NotGormi/Taller_Diseno_Grupo11/iteraciones/iteracion_1/README.md

# Iteración 1 - Concepto Inicial

## Información General

**Fecha:** [23/04/2025]  
**Versión:** v1.0  
**Estado:** Prototipo alpha - Prueba de concepto  
**Avance asociado:** Planificación inicial / Avance #1

---

## Descripción

Primera versión del prototipo, enfocada en validar la factibilidad técnica del concepto.

**Objetivo de esta iteración:**
- Probar conexión de sensores básicos
- Validar comunicación con microcontrolador
- Demostrar concepto de actuación
- Circuito básico en protoboard

---

## Componentes Utilizados

### Hardware
- Microcontrolador: [Modelo]
- Sensores:
  - [Sensor 1]
  - [Sensor 2]
- Actuadores:
  - [Actuador 1]
- Otros: [Lista]

### Software
- IDE: Arduino IDE
- Librerías: [Lista]
- Versión código: v1.0

---

## Fotos del Prototipo

Incluir en esta carpeta:
- `v1_circuito_protoboard.jpg`
- `v1_vista_general.jpg`
- `v1_detalle_conexiones.jpg`

---

## Resultados de Testing Inicial

### Funcionalidad Lograda
✅ [Función 1]  
✅ [Función 2]  
❌ [Función 3 - no funcionó]

### Problemas Identificados

1. **Problema 1:**
   - Descripción: [Detalles]
   - Causa probable: [Análisis]
   - Solución propuesta: [Plan]

2. **Problema 2:**
   - Descripción: [Detalles]
   - Causa probable: [Análisis]
   - Solución propuesta: [Plan]

---

## Aprendizajes

### Técnicos
- [Aprendizaje 1]
- [Aprendizaje 2]

### De Diseño
- [Aprendizaje 1]
- [Aprendizaje 2]

---

## Plan para Iteración 2

### Mejoras Planificadas

**Hardware:**
- [ ] [Mejora 1]
- [ ] [Mejora 2]

**Software:**
- [ ] [Mejora 1]
- [ ] [Mejora 2]

**Diseño:**
- [ ] Iniciar diseño de encapsulado
- [ ] Mejorar ruteo de cables

---

## Archivos en esta Carpeta

- `v1_codigo.ino` - Código de esta versión
- `v1_esquema.png` - Esquema del circuito
- `v1_fotos/` - Fotografías del prototipo
- `v1_notas.txt` - Notas adicionales del equipo
