NotGormi/Taller_Diseno_Grupo11/iteraciones/iteracion_2/README.md

# Iteración 2 - Primera Mejora Significativa

## Información General

**Fecha:** [21/05/2026]  
**Versión:** v2.0  
**Estado:** Prototipo funcional mejorado  
**Avance asociado:** Avance #2

---

## Descripción

Segunda versión del prototipo, incorporando feedback de la iteración 1 y del Avance #1. Incluye mejoras significativas en funcionalidad y primeros pasos en diseño de encapsulado.

**Objetivos de esta iteración:**
- Corregir problemas identificados en v1
- Agregar funcionalidades adicionales
- Iniciar diseño 3D del encapsulado
- Realizar primeras pruebas con usuarios

---

## Cambios Respecto a v1

### Hardware
**Agregado:**
- [Componente nuevo 1]
- [Componente nuevo 2]

**Modificado:**
- [Cambio 1] - Razón: [Justificación]
- [Cambio 2] - Razón: [Justificación]

**Removido:**
- [Componente removido] - Razón: [Justificación]

### Software
**Nuevas funcionalidades:**
- [Feature 1]
- [Feature 2]

**Optimizaciones:**
- [Optimización 1]
- [Optimización 2]

**Bugs corregidos:**
- [Bug 1 de v1]
- [Bug 2 de v1]

### Diseño Mecánico
- Primer diseño de encapsulado en Fusion 360
- Prototipo impreso en 3D
- Integración de componentes en carcasa

---

## Fotos del Prototipo v2

Incluir en esta carpeta:
- `v2_prototipo_completo.jpg`
- `v2_circuito_integrado.jpg`
- `v2_encapsulado_inicial.jpg`
- `v2_testing_usuario.jpg`

---

## Resultados de Testing

### Funcionalidad Lograda
✅ [Función 1]  
✅ [Función 2]  
✅ [Función 3]  
⚠️ [Función 4 - parcial]

### Feedback del Avance #2

**Comentarios del profesor/ayudante:**
1. [Comentario 1]
   - Acción: [Plan de mejora para v3]

2. [Comentario 2]
   - Acción: [Plan de mejora para v3]

### Testing con Usuarios (2-3 personas)

**Resultados cuantitativos:**
- Facilidad de uso promedio: [X/5]
- Satisfacción promedio: [X/5]

**Feedback cualitativo:**
- Positivo: [Comentarios]
- A mejorar: [Comentarios]

---

## Problemas Pendientes

1. **Problema 1:**
   - Descripción: [Detalles]
   - Prioridad: Alta/Media/Baja
   - Plan para v3: [Solución propuesta]

2. **Problema 2:**
   - Descripción: [Detalles]
   - Prioridad: Alta/Media/Baja
   - Plan para v3: [Solución propuesta]

---

## Comparación v1 vs v2

| Aspecto | v1 | v2 | Mejora |
|---|----|----|---|
| Sensores funcionales | 1/1 | 1/1 | ✅ |
| Tiempo de respuesta | 500ms | 200ms | ↓60% |
| Consumo energético | 250mA | 180mA | ↓28% |
| Encapsulado | ❌ | Prototipo | ✅ |

---
