NotGormi/Taller_Diseno_Grupo11/diseno_3d/renders/01_isometrica_posterior_v3.2.png

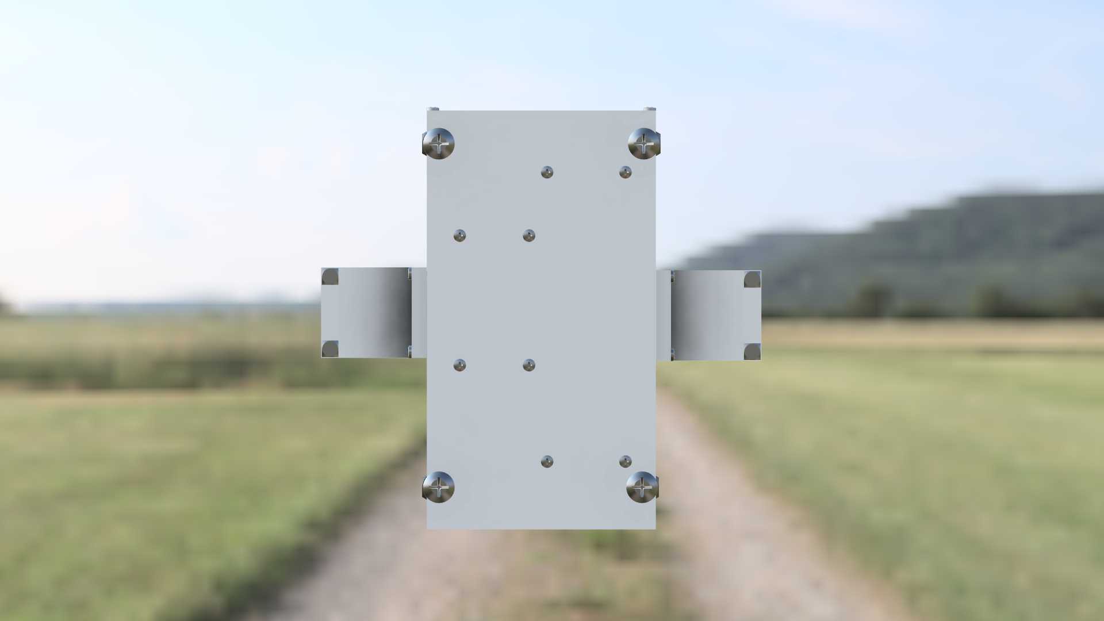
diseno_3d/renders/01_isometrica_posterior_v3.2.png
