NotGormi/Taller_Diseno_Grupo11/hardware/esquemas/esquema_circuito.png

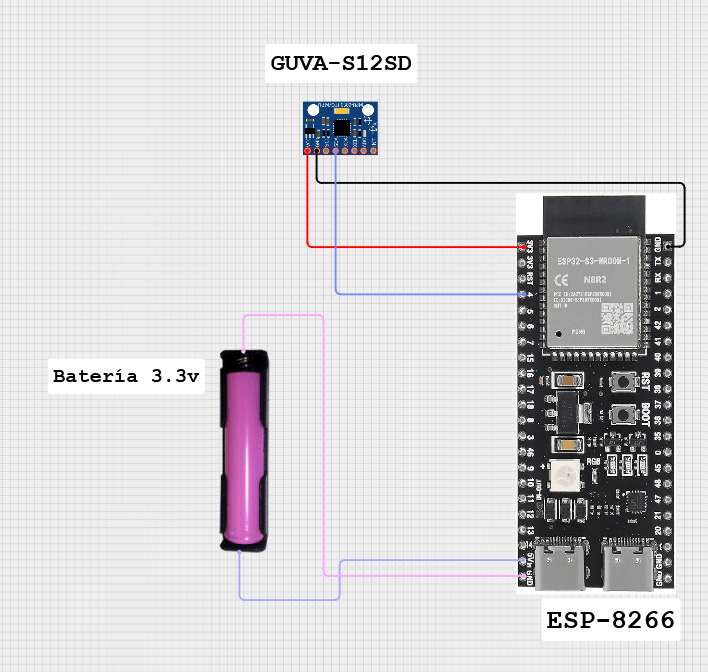
hardware/esquemas/esquema_circuito.png
