NotGormi/Taller_Diseno_Grupo11/software/docs/Untitled Diagram.drawio.png

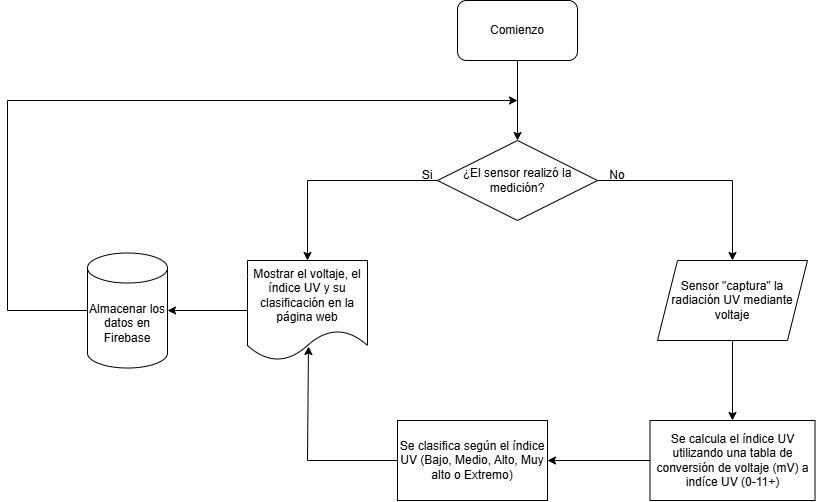
software/docs/Untitled Diagram.drawio.png
